stosem/avr-wt-synth/cad/m3.kicad_sch

## KiCad design cad/m3.kicad_sch (2022-06-24)

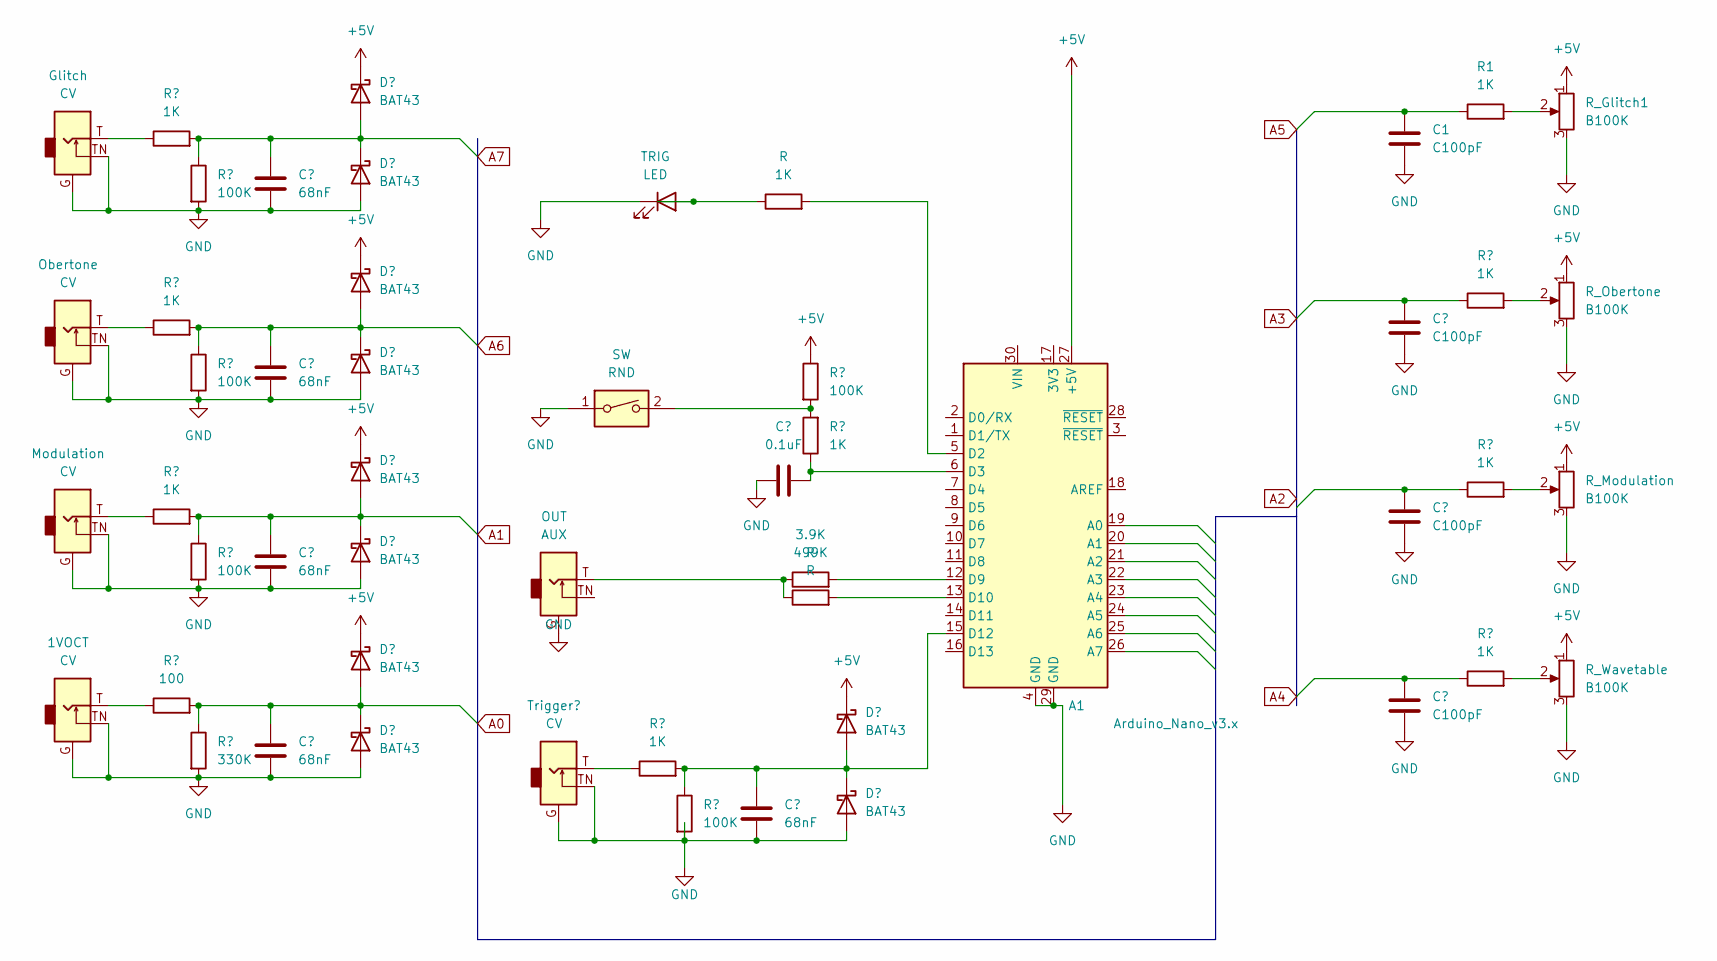
[picture p2: schematic m3.kicad_sch]

Parts:
1VOCT: CV
3.9K, 499K: R
A1: Arduino_Nano_v3.x; Arduino_Nano
C1: C100pF
Glitch: CV
Modulation: CV
OUT: AUX
Obertone: CV
R, R1: 1K
R_Glitch1: B100K
R_Modulation: B100K
R_Obertone: B100K
R_Wavetable: B100K
SW: RND
TRIG: LED

Connections:
+5V: A1.27 (+5V), R_Glitch1.1
GND: A1.4 (GND), A1.29 (GND), R_Glitch1.3
unnamed: 1VOCT.G, 1VOCT.TN
unnamed: 3.9K.1, 499K.1, OUT.T
unnamed: 3.9K.2, A1.12 (D9)
unnamed: 499K.2, A1.13 (D10)
unnamed: A1.5 (D2), R.2
unnamed: C1.1, R1.1
unnamed: Glitch.G, Glitch.TN
unnamed: Modulation.G, Modulation.TN
unnamed: Obertone.G, Obertone.TN
unnamed: R1.2, R_Glitch1.2
unnamed: R.1, TRIG.2 (A)
